philippgurtner/STM32AnalogExtension/Software/Nachberechnugen_DEBUG/SimAusgangsspannung.asc

C1: cap; 1µ
C5: cap; 1µ
C6: cap; 1µ
R1: res; 4.7k
R2: res; .1
R3: res; 120
R4: res; .1
R5: res; .1
R6: res; 2.2K
V1: voltage; 3V
Named nets: 0, VCC, ADC0, ADC1, ADC2
.tran 0 100 90
