philippgurtner/STM32AnalogExtension/ADC-Erweiterung/V0.2.sch

## EAGLE design ADC-Erweiterung/V0.2.sch (2019-12-03)

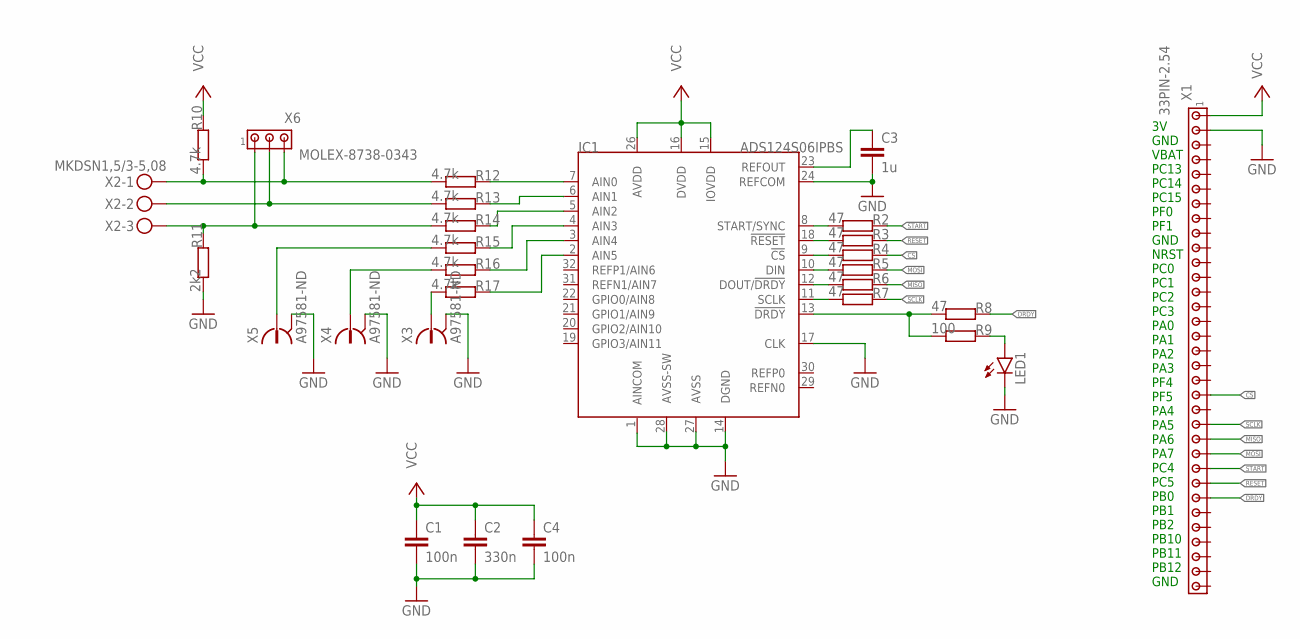
[picture p19: schematic V0.2.sch]

Parts:
C1, C4: 100n; C0603; DIGIKEY_NR 1276-6439-1-ND
C2: 330n; C0603; DIGIKEY_NR 490-6050-1-ND
C3: 1u; C0603; DIGIKEY_NR 1276-1182-1-ND
IC1: ADS124S06IPBS; TQFP32-05; DIGIKEY_NR 296-45188-ND
LED1: LEDSML0603; SML0603; DIGIKEY_NR 475-3118-1-ND
R2, R3, R4, R5, R6, R7, R8: 47; R0603; DIGIKEY_NR 311-470GRCT-ND
R9: 100; R0603; DIGIKEY_NR 311-100DCT-ND
R10, R12, R13, R14, R15, R16, R17: 4.7k; R0603; DIGIKEY_NR 311-4.70KHRCT-ND
R11: 2k2; R0805W; DIGIKEY_NR 408-1635-1-ND
X1: 33PIN-2.54; 1X33; DIGIKEY_NR 609-2223-ND
X2: MKDSN1,5/3-5,08; DIGIKEY_NR 277-14503-ND
X3, X4, X5: A97581-ND; 1634503; DIGIKEY_NR A97581-ND
X6: MOLEX-8738-0343; MOLEX-87438-0343; DIGIKEY_NR WM7647CT-ND

Connections:
CS: R4.2, X1.20
DRDY: R8.2, X1.27
GND: C1.2, C2.2, C3.2, C4.2, IC1.1 (AINCOM), IC1.14 (DGND), IC1.17 (CLK), IC1.24 (REFCOM), IC1.27 (AVSS), IC1.28 (AVSS-SW), LED1.C, R11.1, X1.2, X3.2, X4.2, X5.2
MISO: R6.2, X1.23
MOSI: R5.2, X1.24
unnamed: IC1.8 (START/SYNC), R2.1
unnamed: IC1.18 (!RESET), R3.1
unnamed: IC1.9 (!CS), R4.1
unnamed: IC1.10 (DIN), R5.1
unnamed: IC1.12 (DOUT/!DRDY), R6.1
unnamed: IC1.11 (SCLK), R7.1
unnamed: IC1.13 (!DRDY), R8.1, R9.1
unnamed: R10.1, R12.1, X2.1, X6.3
unnamed: R13.1, X2.2, X6.2
unnamed: R11.2, R14.1, X2.3, X6.1
unnamed: R15.1, X5.1
unnamed: IC1.3 (AIN4), R16.2
unnamed: IC1.2 (AIN5), R17.2
unnamed: LED1.A, R9.2
unnamed: C3.1, IC1.23 (REFOUT)
unnamed: IC1.4 (AIN3), R15.2
unnamed: R16.1, X4.1
unnamed: R17.1, X3.1
unnamed: IC1.5 (AIN2), R14.2
unnamed: IC1.7 (AIN0), R12.2
unnamed: IC1.6 (AIN1), R13.2
RESET: R3.2, X1.26
SCLK: R7.2, X1.22
START: R2.2, X1.25
VCC: C1.1, C2.1, C4.1, IC1.15 (IOVDD), IC1.16 (DVDD), IC1.26 (AVDD), R10.2, X1.1

Notes on the sheet:
3V GND VBAT PC13 PC14 PC15 PF0 PF1 GND NRST PC0 PC1 PC2 PC3 PA0 PA1 PA2 PA3 PF4 PF5 PA4 PA5 PA6 PA7 PC4 PC5 PB0 PB1 PB2 PB10 PB11 PB12 GND
